Emnabz909/Pseudo_GPS_for_Romi_Bots/CAD Files/STL Files/CamSpacer.STL

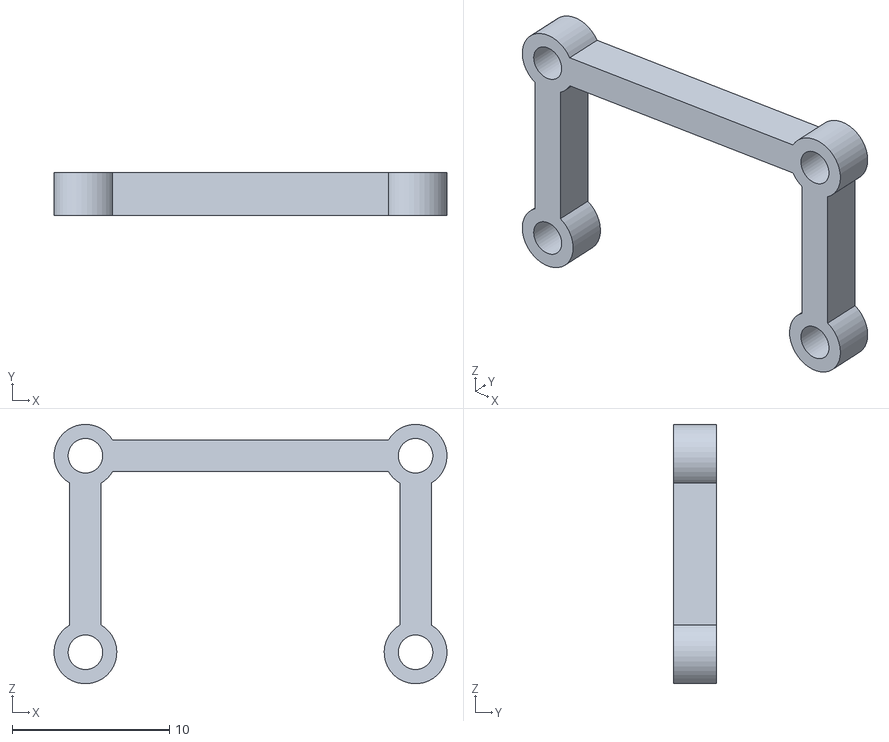
[picture p46: CAD file, 2024-11-21]
CAD Files/STL Files/CamSpacer.STL
25.0 x 2.75 x 16.5
