Emnabz909/Pseudo_GPS_for_Romi_Bots/CAD Files/SolidWorks Parts/2310 Raspi_Cam_Module_3.SLDPRT

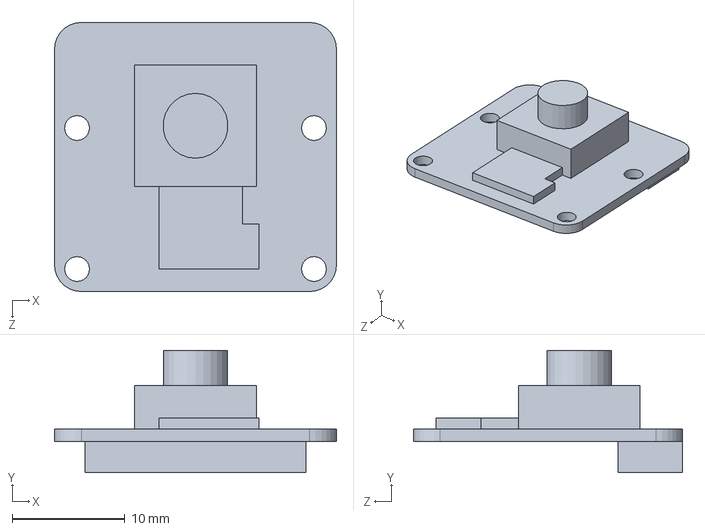
[picture p47: CAD file, 2024-11-21]
CAD Files/SolidWorks Parts/2310 Raspi_Cam_Module_3.SLDPRT
25.0 x 10.9 x 23.9 mm
