Emnabz909/Pseudo_GPS_for_Romi_Bots/CAD Files/SolidWorks Parts/Assemblies/Testbench_stands.SLDASM

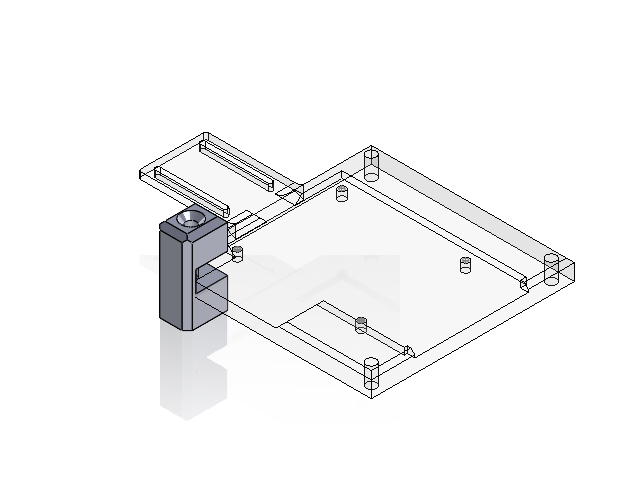
[picture p49: CAD file, 2024-11-21]
CAD Files/SolidWorks Parts/Assemblies/Testbench_stands.SLDASM
210 FrameBase
testStands^Testbench_stands
